monkzzz/Lotus58/Lotus 58 TRRS/v1.30/bom/readme.md

# Interactive BOM
To view the interactive bom, use the html preview link here: http://htmlpreview.github.io/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

**Please note** that the BOM relies on the PCB manufacturing files, and shows the various positions for both sides. 

Because of the dual sided design, some of the quantities for the various parts may need be doubled for a full two handed build, as some parts are counted only once, and some may not need too, as they are possible to position on both sides and counted correctly. 

This is impossible to correct without making the files unusable for PCB manufacture, so you you will have to use common sense and first grade math to get the correct amounts. 

The same applies to encoders OLED's etc, that aren't counted correctly, and varies according to your selected options.
